LikeClockwork/LargeWordClock/KiCad/LargeKickstarter/SVG/button_section.png

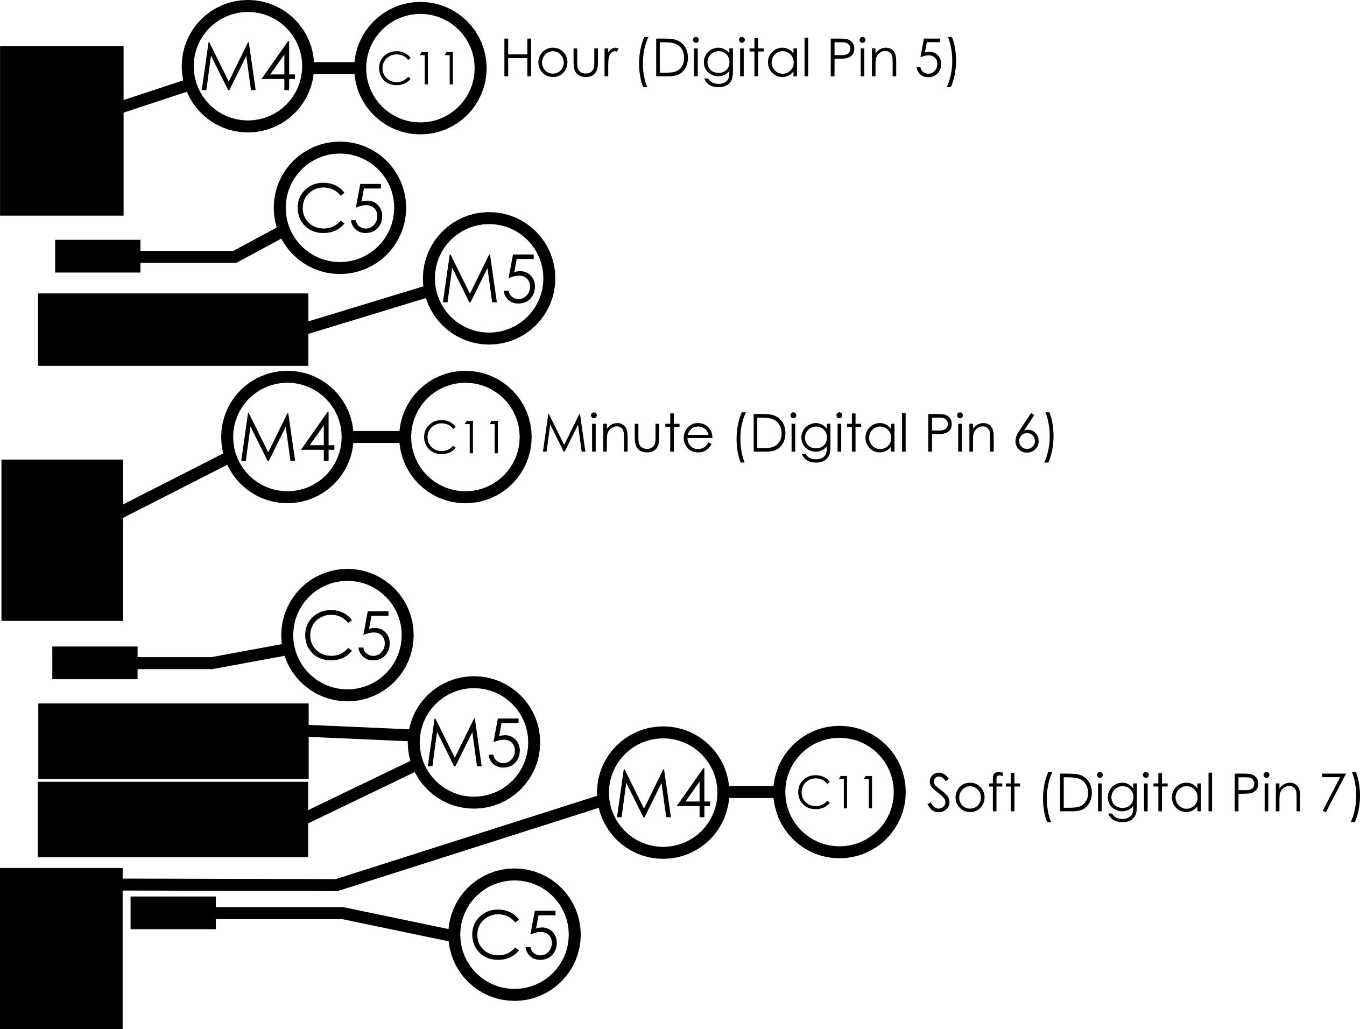
KiCad/LargeKickstarter/SVG/button_section.png
