LikeClockwork/LargeWordClock/KiCad/LargeKickstarter/SVG/Proto_area.png

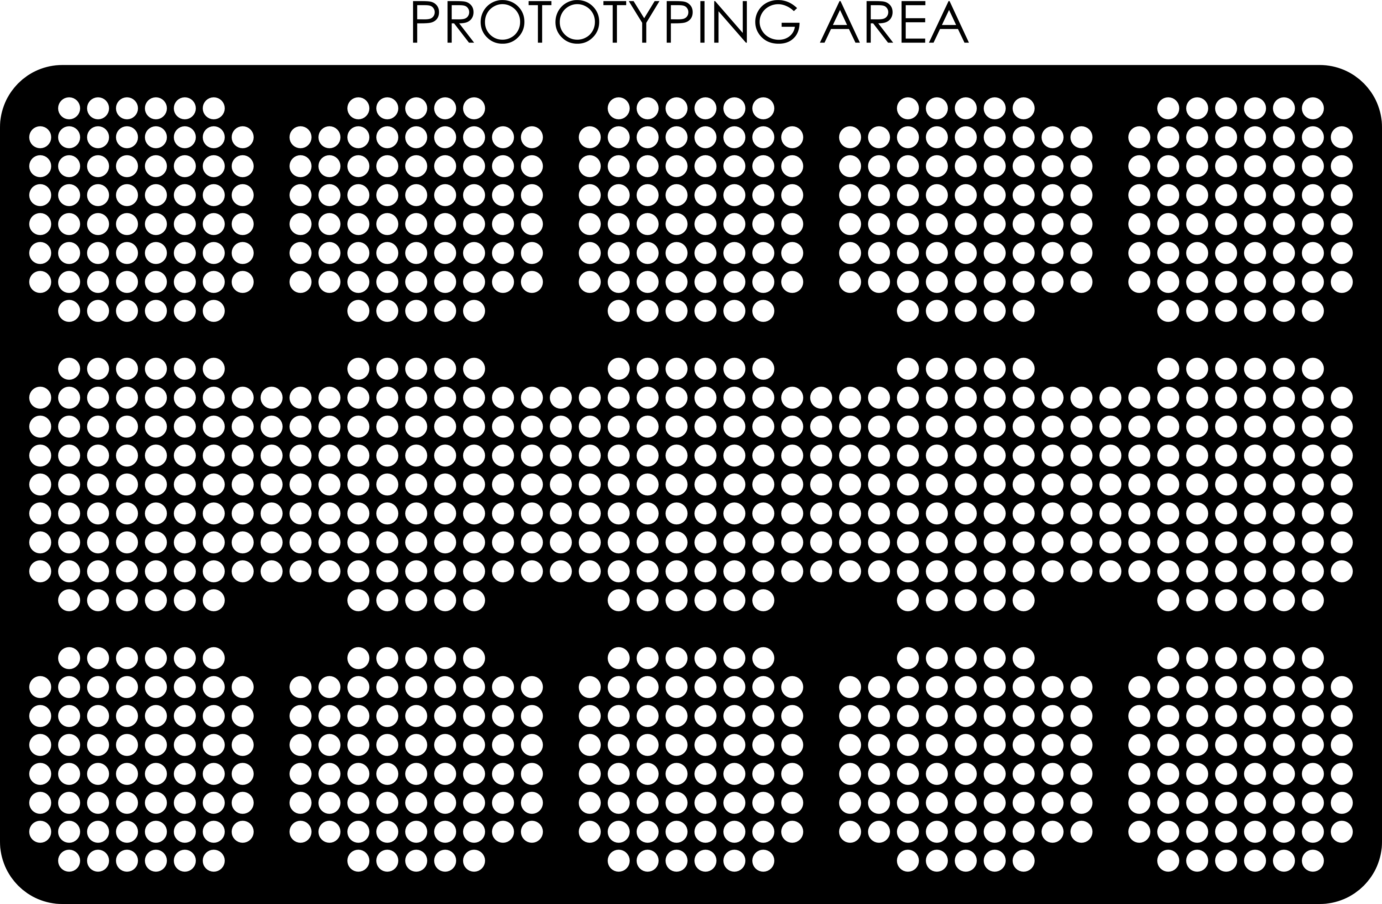
KiCad/LargeKickstarter/SVG/Proto_area.png
