LikeClockwork/LargeWordClock/KiCad/LargeKickstarter/SVG/shield_footprint.png

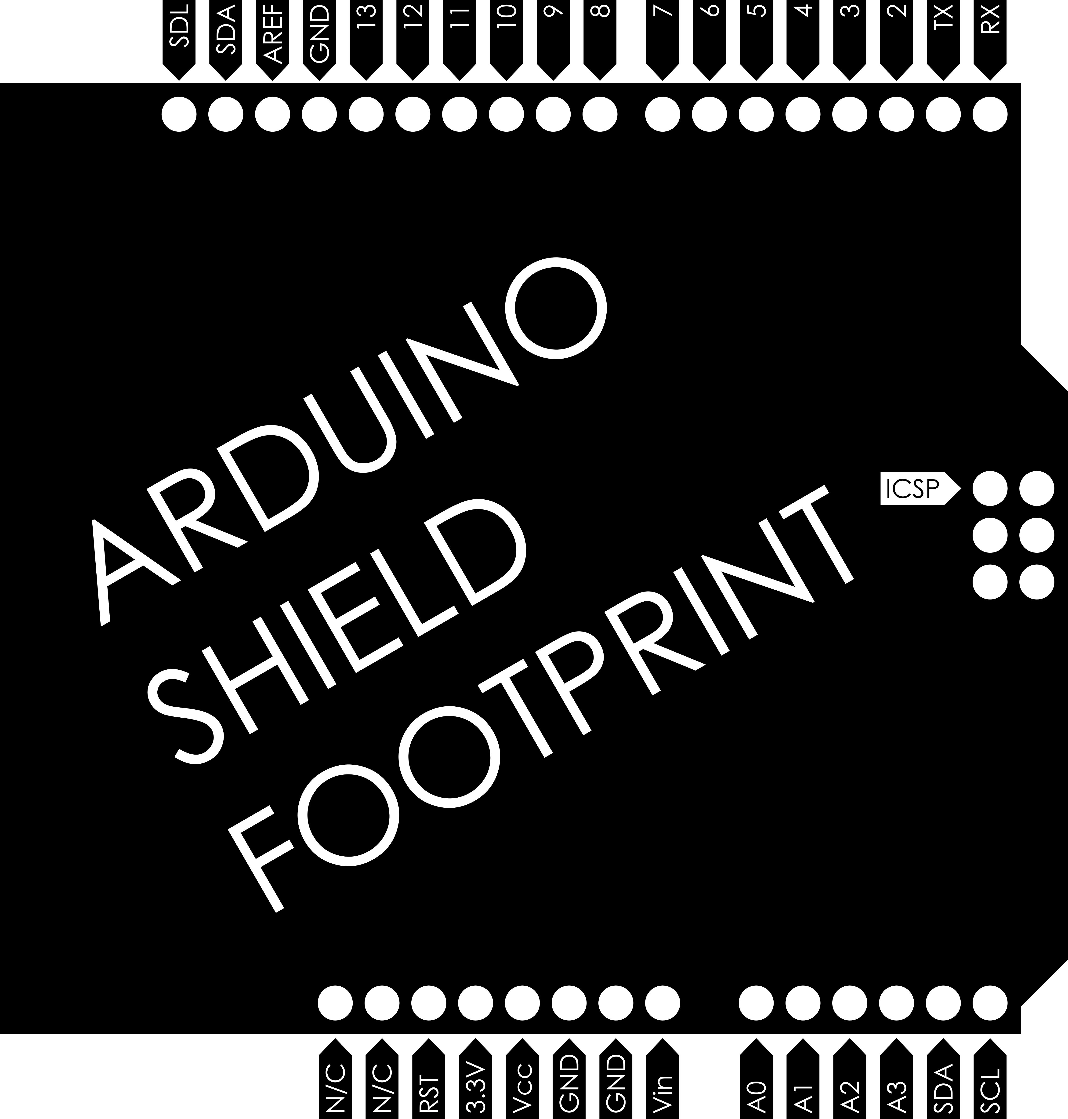
KiCad/LargeKickstarter/SVG/shield_footprint.png
