LikeClockwork/LargeWordClock/KiCad/LargeKickstarter/LargeKickstarter.sch

## KiCad design KiCad/LargeKickstarter/LargeKickstarter.sch (2015-11-24)

Schematic: LargeKickstarter.sch

Parts:
0-0, 0-1, 0-2, 0-3, 0-4, 0-5, 0-6, 0-7, 0-8, 0-9, 0-10, 0-11, 0-12, 0-13, 0-14, 0-15, 0-16, 0-17, 0-18, 0-19, 0-20, 0-21, 0-22, 0-23, 0-24, 0-25, 0-26, 0-27, 0-28, 0-29, 0-30, 0-31, 1-0, 1-1, 1-2, 1-3, 1-4, 1-5, 1-6, 1-7, 1-8, 1-9, 1-10, 1-11, 1-12, 1-13, 1-14, 1-15, 1-16, 1-17, 1-18, 1-19, 1-20, 1-21, 1-22, 1-23, 1-24, 1-25, 1-26, 1-27, 1-28, 1-29, 1-30, 1-31, 2-0, 2-1, 2-2, 2-3, 2-4, 2-5, 2-6, 2-7, 2-8, 2-9, 2-10, 2-11, 2-12, 2-13, 2-14, 2-15, 2-16, 2-17, 2-18, 2-19, 2-20, 2-21, 2-22, 2-23, 2-24, 2-25, 2-26, 2-27, 2-28, 2-29, 2-30, 2-31, 3-0, 3-1, 3-2, 3-3, 3-4, 3-5, 3-6, 3-7, 3-8, 3-9, 3-10, 3-11, 3-12, 3-13, 3-14, 3-15, 3-16, 3-17, 3-18, 3-19, 3-20, 3-21, 3-22, 3-23, 3-24, 3-25, 3-26, 3-27, 3-28, 3-29, 3-30, 3-31, 4-0, 4-1, 4-2, 4-3, 4-4, 4-5, 4-6, 4-7, 4-8, 4-9, 4-10, 4-11, 4-12, 4-13, 4-14, 4-15, 4-16, 4-17, 4-18, 4-19, 4-20, 4-21, 4-22, 4-23, 4-24, 4-25, 4-26, 4-27, 4-28, 4-29, 4-30, 4-31, 5-0, 5-1, 5-2, 5-3, 5-4, 5-5, 5-6, 5-7, 5-8, 5-9, 5-10, 5-11, 5-12, 5-13, 5-14, 5-15, 5-16, 5-17, 5-18, 5-19, 5-20, 5-21, 5-22, 5-23, 5-24, 5-25, 5-26, 5-27, 5-28, 5-29, 5-30, 5-31, 6-0, 6-1, 6-2, 6-3, 6-4, 6-5, 6-6, 6-7, 6-8, 6-9, 6-10, 6-11, 6-12, 6-13, 6-14, 6-15, 6-16, 6-17, 6-18, 6-19, 6-20, 6-21, 6-22, 6-23, 6-24, 6-25, 6-26, 6-27, 6-28, 6-29, 6-30, 6-31, 7-0, 7-1, 7-2, 7-3, 7-4, 7-5, 7-6, 7-7, 7-8, 7-9, 7-10, 7-11, 7-12, 7-13, 7-14, 7-15, 7-16, 7-17, 7-18, 7-19, 7-20, 7-21, 7-22, 7-23, 7-24, 7-25, 7-26, 7-27, 7-28, 7-29, 7-30, 7-31, 8-0, 8-1, 8-2, 8-3, 8-4, 8-5, 8-6, 8-7, 8-8, 8-9, 8-10, 8-11, 8-12, 8-13, 8-14, 8-15, 8-16, 8-17, 8-18, 8-19, 8-20, 8-21, 8-22, 8-23, 8-24, 8-25, 8-26, 8-27, 8-28, 8-29, 8-30, 8-31, 9-0, 9-1, 9-2, 9-3, 9-4, 9-5, 9-6, 9-7, 9-8, 9-9, 9-10, 9-11, 9-12, 9-13, 9-14, 9-15, 9-16, 9-17, 9-18, 9-19, 9-20, 9-21, 9-22, 9-23, 9-24, 9-25, 9-26, 9-27, 9-28, 9-29, 9-30, 9-31, 10-0, 10-1, 10-2, 10-3, 10-4, 10-5, 10-6, 10-7, 10-8, 10-9, 10-10, 10-11, 10-12, 10-13, 10-14, 10-15, 10-16, 10-17, 10-18, 10-19, 10-20, 10-21, 10-22, 10-23, 10-24, 10-25, 10-26, 10-27, 10-28, 10-29, 10-30, 10-31, 11-0, 11-1, 11-2, 11-3, 11-4, 11-5, 11-6, 11-7, 11-8, 11-9, 11-10, 11-11, 11-12, 11-13, 11-14, 11-15, 11-16, 11-17, 11-18, 11-19, 11-20, 11-21, 11-22, 11-23, 11-24, 11-25, 11-26, 11-27, 11-28, 11-29, 11-30, 11-31, 12-0, 12-1, 12-2, 12-3, 12-4, 12-5, 12-6, 12-7, 12-8, 12-9, 12-10, 12-11, 12-12, 12-13, 12-14, 12-15, 12-16, 12-17, 12-18, 12-19, 12-20, 12-21, 12-22, 12-23, 12-24, 12-25, 12-26, 12-27, 12-28, 12-29, 12-30, 12-31, 13-0, 13-1, 13-2, 13-3, 13-4, 13-5, 13-6, 13-7, 13-8, 13-9, 13-10, 13-11, 13-12, 13-13, 13-14, 13-15, 13-16, 13-17, 13-18, 13-19, 13-20, 13-21, 13-22, 13-23, 13-24, 13-25, 13-26, 13-27, 13-28, 13-29, 13-30, 13-31, 14-0, 14-1, 14-2, 14-3, 14-4, 14-5, 14-6, 14-7, 14-8, 14-9, 14-10, 14-11, 14-12, 14-13, 14-14, 14-15, 14-16, 14-17, 14-18, 14-19, 14-20, 14-21, 14-22, 14-23, 14-24, 14-25, 14-26, 14-27, 14-28, 14-29, 14-30, 14-31, 15-0, 15-1, 15-2, 15-3, 15-4, 15-5, 15-6, 15-7, 15-8, 15-9, 15-10, 15-11, 15-12, 15-13, 15-14, 15-15, 15-16, 15-17, 15-18, 15-19, 15-20, 15-21, 15-22, 15-23, 15-24, 15-25, 15-26, 15-27, 15-28, 15-29, 15-30, 15-31: LED; SMD_LED_PLCC_2
BT1: BATTERY; BATTCOM_20MM_PTH
C1, C4, C5, C6, C7, C8: 0.1uF; C_0603_HandSoldering
C2: 10uF; Elko_vert_11.2x7.5mm_RM2.5_CopperClear
C3: 1uF; Elko_vert_11.2x7.5mm_RM2.5_CopperClear
D1: DIODE; Diode-SMA_Handsoldering
D2, D3, D4, D5: DIODE; SOD-323
D6: DIODE; Diode_DO-41_SOD81_Horizontal_RM10
JP1, JP2, JP3, JP4, JP5, JP6, JP7, JP8, JP9, JP10, JP11, JP12: JUMPER; solder_jumper
P1: CONN_01X03; Diode_TO-220_Dual_CommonCathode_Horizontal_LargePads
P2: CONN_01X02; Pin_Header_Straight_1x02
P3: CONN_01X05; Pin_Header_Straight_1x05
P4: CONN_02X03; Pin_Header_Straight_2x03
P5: CONN_01X06; Pin_Header_Straight_1x06
R1, R2, R4, R5, R7: 10K; R_0603_HandSoldering
R3, R6, R8, R9, R10, R11, R12, R13, R14, R15, R16, R17: 47K; R_0603_HandSoldering
R18, R19, R20: 10K; Resistor_Horizontal_RM10mm
SW1: HOUR; TACTILE-PTH-SIDEEZ
SW2: MIN; TACTILE-PTH-SIDEEZ
SW4: SOFT; TACTILE-PTH-SIDEEZ
U1, U4, U10, U12: HT16K33; SO28W
U2: DS3231; SOIC-16_7.5x10.3mm_Pitch1.27mm
U3: ATMEGA328-TQFP; TQFP32-08
U5, U6, U9, U11: HT16K33_BOUT; HT16K33_Breakout
U7: Arduino_Nano
U8: UNO_FOOTPRINT; shield_footprint

Connections:
2: U3.32 (2), U7.5 (2), U8.30 (2)
3: U3.1 (3), U7.6 (3), U8.29 (3)
3.3V: U7.29 (3.3V), U8.4 (3.3V)
4: U3.2 (4), U7.7 (4), U8.28 (4)
5: R1.1, R18.1, SW1.2, U3.9 (5), U7.8 (5), U8.27 (5)
6: R2.1, R19.1, SW2.2, U3.10 (6), U7.9 (6), U8.26 (6)
7: R5.1, R20.1, SW4.2, U3.11 (7), U7.10 (7), U8.25 (7)
8: U3.12 (8), U7.11 (8), U8.24 (8)
9: U3.13 (9), U7.12 (9), U8.23 (9)
10: U3.14 (10), U7.13 (10/SS), U8.22 (10)
A0: U3.23 (A0), U7.27 (A0), U8.9 (A0)
A1: U3.24 (A1), U7.26 (A1), U8.10 (A1)
A2: U3.25 (A2), U7.25 (A2), U8.11 (A2)
A3: U3.26 (A3), U7.24 (A3), U8.12 (A3)
A6: U3.19 (A6), U7.21 (A6)
A7: U3.22 (A7), U7.20 (A7)
AREF: U3.20 (AREF), U7.28 (AREF), U8.17 (AREF)
COM-0-0: 0-0.2 (K), 1-0.2 (K), 2-0.2 (K), 3-0.2 (K), 4-0.2 (K), 5-0.2 (K), 6-0.2 (K), 7-0.2 (K), 8-0.2 (K), 9-0.2 (K), 10-0.2 (K), 11-0.2 (K), 12-0.2 (K), 13-0.2 (K), 14-0.2 (K), 15-0.2 (K), D3.2 (A), U1.2 (COM0/AD), U5.2 (COM0/A0)
COM-0-1: 0-1.2 (K), 1-1.2 (K), 2-1.2 (K), 3-1.2 (K), 4-1.2 (K), 5-1.2 (K), 6-1.2 (K), 7-1.2 (K), 8-1.2 (K), 9-1.2 (K), 10-1.2 (K), 11-1.2 (K), 12-1.2 (K), 13-1.2 (K), 14-1.2 (K), 15-1.2 (K), U1.3 (COM1), U5.3 (COM1)
COM-0-2: 0-2.2 (K), 1-2.2 (K), 2-2.2 (K), 3-2.2 (K), 4-2.2 (K), 5-2.2 (K), 6-2.2 (K), 7-2.2 (K), 8-2.2 (K), 9-2.2 (K), 10-2.2 (K), 11-2.2 (K), 12-2.2 (K), 13-2.2 (K), 14-2.2 (K), 15-2.2 (K), U1.4 (COM2), U5.4 (COM2)
COM-0-3: 0-3.2 (K), 1-3.2 (K), 2-3.2 (K), 3-3.2 (K), 4-3.2 (K), 5-3.2 (K), 6-3.2 (K), 7-3.2 (K), 8-3.2 (K), 9-3.2 (K), 10-3.2 (K), 11-3.2 (K), 12-3.2 (K), 13-3.2 (K), 14-3.2 (K), 15-3.2 (K), U1.5 (COM3), U5.5 (COM3)
COM-0-4: 0-4.2 (K), 1-4.2 (K), 2-4.2 (K), 3-4.2 (K), 4-4.2 (K), 5-4.2 (K), 6-4.2 (K), 7-4.2 (K), 8-4.2 (K), 9-4.2 (K), 10-4.2 (K), 11-4.2 (K), 12-4.2 (K), 13-4.2 (K), 14-4.2 (K), 15-4.2 (K), U1.6 (COM4), U5.6 (COM4)
COM-0-5: 0-5.2 (K), 1-5.2 (K), 2-5.2 (K), 3-5.2 (K), 4-5.2 (K), 5-5.2 (K), 6-5.2 (K), 7-5.2 (K), 8-5.2 (K), 9-5.2 (K), 10-5.2 (K), 11-5.2 (K), 12-5.2 (K), 13-5.2 (K), 14-5.2 (K), 15-5.2 (K), U1.7 (COM5), U5.7 (COM5)
COM-0-6: 0-6.2 (K), 1-6.2 (K), 2-6.2 (K), 3-6.2 (K), 4-6.2 (K), 5-6.2 (K), 6-6.2 (K), 7-6.2 (K), 8-6.2 (K), 9-6.2 (K), 10-6.2 (K), 11-6.2 (K), 12-6.2 (K), 13-6.2 (K), 14-6.2 (K), 15-6.2 (K), U1.8 (COM6), U5.8 (COM6)
COM-0-7: 0-7.2 (K), 1-7.2 (K), 2-7.2 (K), 3-7.2 (K), 4-7.2 (K), 5-7.2 (K), 6-7.2 (K), 7-7.2 (K), 8-7.2 (K), 9-7.2 (K), 10-7.2 (K), 11-7.2 (K), 12-7.2 (K), 13-7.2 (K), 14-7.2 (K), 15-7.2 (K), U1.9 (COM7), U5.9 (COM7)
COM-1-0: 0-8.2 (K), 1-8.2 (K), 2-8.2 (K), 3-8.2 (K), 4-8.2 (K), 5-8.2 (K), 6-8.2 (K), 7-8.2 (K), 8-8.2 (K), 9-8.2 (K), 10-8.2 (K), 11-8.2 (K), 12-8.2 (K), 13-8.2 (K), 14-8.2 (K), 15-8.2 (K), D2.2 (A), U4.2 (COM0/AD), U6.2 (COM0/A0)
COM-1-1: 0-9.2 (K), 1-9.2 (K), 2-9.2 (K), 3-9.2 (K), 4-9.2 (K), 5-9.2 (K), 6-9.2 (K), 7-9.2 (K), 8-9.2 (K), 9-9.2 (K), 10-9.2 (K), 11-9.2 (K), 12-9.2 (K), 13-9.2 (K), 14-9.2 (K), 15-9.2 (K), U4.3 (COM1), U6.3 (COM1)
COM-1-2: 0-10.2 (K), 1-10.2 (K), 2-10.2 (K), 3-10.2 (K), 4-10.2 (K), 5-10.2 (K), 6-10.2 (K), 7-10.2 (K), 8-10.2 (K), 9-10.2 (K), 10-10.2 (K), 11-10.2 (K), 12-10.2 (K), 13-10.2 (K), 14-10.2 (K), 15-10.2 (K), U4.4 (COM2), U6.4 (COM2)
COM-1-3: 0-11.2 (K), 1-11.2 (K), 2-11.2 (K), 3-11.2 (K), 4-11.2 (K), 5-11.2 (K), 6-11.2 (K), 7-11.2 (K), 8-11.2 (K), 9-11.2 (K), 10-11.2 (K), 11-11.2 (K), 12-11.2 (K), 13-11.2 (K), 14-11.2 (K), 15-11.2 (K), U4.5 (COM3), U6.5 (COM3)
COM-1-4: 0-12.2 (K), 1-12.2 (K), 2-12.2 (K), 3-12.2 (K), 4-12.2 (K), 5-12.2 (K), 6-12.2 (K), 7-12.2 (K), 8-12.2 (K), 9-12.2 (K), 10-12.2 (K), 11-12.2 (K), 12-12.2 (K), 13-12.2 (K), 14-12.2 (K), 15-12.2 (K), U4.6 (COM4), U6.6 (COM4)
COM-1-5: 0-13.2 (K), 1-13.2 (K), 2-13.2 (K), 3-13.2 (K), 4-13.2 (K), 5-13.2 (K), 6-13.2 (K), 7-13.2 (K), 8-13.2 (K), 9-13.2 (K), 10-13.2 (K), 11-13.2 (K), 12-13.2 (K), 13-13.2 (K), 14-13.2 (K), 15-13.2 (K), U4.7 (COM5), U6.7 (COM5)
COM-1-6: 0-14.2 (K), 1-14.2 (K), 2-14.2 (K), 3-14.2 (K), 4-14.2 (K), 5-14.2 (K), 6-14.2 (K), 7-14.2 (K), 8-14.2 (K), 9-14.2 (K), 10-14.2 (K), 11-14.2 (K), 12-14.2 (K), 13-14.2 (K), 14-14.2 (K), 15-14.2 (K), U4.8 (COM6), U6.8 (COM6)
COM-1-7: 0-15.2 (K), 1-15.2 (K), 2-15.2 (K), 3-15.2 (K), 4-15.2 (K), 5-15.2 (K), 6-15.2 (K), 7-15.2 (K), 8-15.2 (K), 9-15.2 (K), 10-15.2 (K), 11-15.2 (K), 12-15.2 (K), 13-15.2 (K), 14-15.2 (K), 15-15.2 (K), U4.9 (COM7), U6.9 (COM7)
COM-2-0: 0-16.2 (K), 1-16.2 (K), 2-16.2 (K), 3-16.2 (K), 4-16.2 (K), 5-16.2 (K), 6-16.2 (K), 7-16.2 (K), 8-16.2 (K), 9-16.2 (K), 10-16.2 (K), 11-16.2 (K), 12-16.2 (K), 13-16.2 (K), 14-16.2 (K), 15-16.2 (K), D4.2 (A), U9.2 (COM0/A0), U10.2 (COM0/AD)
COM-2-1: 0-17.2 (K), 1-17.2 (K), 2-17.2 (K), 3-17.2 (K), 4-17.2 (K), 5-17.2 (K), 6-17.2 (K), 7-17.2 (K), 8-17.2 (K), 9-17.2 (K), 10-17.2 (K), 11-17.2 (K), 12-17.2 (K), 13-17.2 (K), 14-17.2 (K), 15-17.2 (K), U9.3 (COM1), U10.3 (COM1)
COM-2-2: 0-18.2 (K), 1-18.2 (K), 2-18.2 (K), 3-18.2 (K), 4-18.2 (K), 5-18.2 (K), 6-18.2 (K), 7-18.2 (K), 8-18.2 (K), 9-18.2 (K), 10-18.2 (K), 11-18.2 (K), 12-18.2 (K), 13-18.2 (K), 14-18.2 (K), 15-18.2 (K), U9.4 (COM2), U10.4 (COM2)
COM-2-3: 0-19.2 (K), 1-19.2 (K), 2-19.2 (K), 3-19.2 (K), 4-19.2 (K), 5-19.2 (K), 6-19.2 (K), 7-19.2 (K), 8-19.2 (K), 9-19.2 (K), 10-19.2 (K), 11-19.2 (K), 12-19.2 (K), 13-19.2 (K), 14-19.2 (K), 15-19.2 (K), U9.5 (COM3), U10.5 (COM3)
COM-2-4: 0-20.2 (K), 1-20.2 (K), 2-20.2 (K), 3-20.2 (K), 4-20.2 (K), 5-20.2 (K), 6-20.2 (K), 7-20.2 (K), 8-20.2 (K), 9-20.2 (K), 10-20.2 (K), 11-20.2 (K), 12-20.2 (K), 13-20.2 (K), 14-20.2 (K), 15-20.2 (K), U9.6 (COM4), U10.6 (COM4)
COM-2-5: 0-21.2 (K), 1-21.2 (K), 2-21.2 (K), 3-21.2 (K), 4-21.2 (K), 5-21.2 (K), 6-21.2 (K), 7-21.2 (K), 8-21.2 (K), 9-21.2 (K), 10-21.2 (K), 11-21.2 (K), 12-21.2 (K), 13-21.2 (K), 14-21.2 (K), 15-21.2 (K), U9.7 (COM5), U10.7 (COM5)
COM-2-6: 0-22.2 (K), 1-22.2 (K), 2-22.2 (K), 3-22.2 (K), 4-22.2 (K), 5-22.2 (K), 6-22.2 (K), 7-22.2 (K), 8-22.2 (K), 9-22.2 (K), 10-22.2 (K), 11-22.2 (K), 12-22.2 (K), 13-22.2 (K), 14-22.2 (K), 15-22.2 (K), U9.8 (COM6), U10.8 (COM6)
COM-2-7: 0-23.2 (K), 1-23.2 (K), 2-23.2 (K), 3-23.2 (K), 4-23.2 (K), 5-23.2 (K), 6-23.2 (K), 7-23.2 (K), 8-23.2 (K), 9-23.2 (K), 10-23.2 (K), 11-23.2 (K), 12-23.2 (K), 13-23.2 (K), 14-23.2 (K), 15-23.2 (K), U9.9 (COM7), U10.9 (COM7)
COM-3-0: 0-24.2 (K), 1-24.2 (K), 2-24.2 (K), 3-24.2 (K), 4-24.2 (K), 5-24.2 (K), 6-24.2 (K), 7-24.2 (K), 8-24.2 (K), 9-24.2 (K), 10-24.2 (K), 11-24.2 (K), 12-24.2 (K), 13-24.2 (K), 14-24.2 (K), 15-24.2 (K), D5.2 (A), U11.2 (COM0/A0), U12.2 (COM0/AD)
COM-3-1: 0-25.2 (K), 1-25.2 (K), 2-25.2 (K), 3-25.2 (K), 4-25.2 (K), 5-25.2 (K), 6-25.2 (K), 7-25.2 (K), 8-25.2 (K), 9-25.2 (K), 10-25.2 (K), 11-25.2 (K), 12-25.2 (K), 13-25.2 (K), 14-25.2 (K), 15-25.2 (K), U11.3 (COM1), U12.3 (COM1)
COM-3-2: 0-26.2 (K), 1-26.2 (K), 2-26.2 (K), 3-26.2 (K), 4-26.2 (K), 5-26.2 (K), 6-26.2 (K), 7-26.2 (K), 8-26.2 (K), 9-26.2 (K), 10-26.2 (K), 11-26.2 (K), 12-26.2 (K), 13-26.2 (K), 14-26.2 (K), 15-26.2 (K), U11.4 (COM2), U12.4 (COM2)
COM-3-3: 0-27.2 (K), 1-27.2 (K), 2-27.2 (K), 3-27.2 (K), 4-27.2 (K), 5-27.2 (K), 6-27.2 (K), 7-27.2 (K), 8-27.2 (K), 9-27.2 (K), 10-27.2 (K), 11-27.2 (K), 12-27.2 (K), 13-27.2 (K), 14-27.2 (K), 15-27.2 (K), U11.5 (COM3), U12.5 (COM3)
COM-3-4: 0-28.2 (K), 1-28.2 (K), 2-28.2 (K), 3-28.2 (K), 4-28.2 (K), 5-28.2 (K), 6-28.2 (K), 7-28.2 (K), 8-28.2 (K), 9-28.2 (K), 10-28.2 (K), 11-28.2 (K), 12-28.2 (K), 13-28.2 (K), 14-28.2 (K), 15-28.2 (K), U11.6 (COM4), U12.6 (COM4)
COM-3-5: 0-29.2 (K), 1-29.2 (K), 2-29.2 (K), 3-29.2 (K), 4-29.2 (K), 5-29.2 (K), 6-29.2 (K), 7-29.2 (K), 8-29.2 (K), 9-29.2 (K), 10-29.2 (K), 11-29.2 (K), 12-29.2 (K), 13-29.2 (K), 14-29.2 (K), 15-29.2 (K), U11.7 (COM5), U12.7 (COM5)
COM-3-6: 0-30.2 (K), 1-30.2 (K), 2-30.2 (K), 3-30.2 (K), 4-30.2 (K), 5-30.2 (K), 6-30.2 (K), 7-30.2 (K), 8-30.2 (K), 9-30.2 (K), 10-30.2 (K), 11-30.2 (K), 12-30.2 (K), 13-30.2 (K), 14-30.2 (K), 15-30.2 (K), U11.8 (COM6), U12.8 (COM6)
COM-3-7: 0-31.2 (K), 1-31.2 (K), 2-31.2 (K), 3-31.2 (K), 4-31.2 (K), 5-31.2 (K), 6-31.2 (K), 7-31.2 (K), 8-31.2 (K), 9-31.2 (K), 10-31.2 (K), 11-31.2 (K), 12-31.2 (K), 13-31.2 (K), 14-31.2 (K), 15-31.2 (K), U11.9 (COM7), U12.9 (COM7)
GND: BT1.2 (-), C1.2, C2.2, C3.2, C4.2, C5.2, C6.2, C7.2, C8.2, P1.2, P2.1, P3.GND (P5), P4.6, P5.6, R1.2, R2.2, R5.2, R18.2, R19.2, R20.2, U1.1 (GND), U2.5 (N/C), U2.6 (N/C), U2.7 (N/C), U2.8 (N/C), U2.9 (N/C), U2.10 (N/C), U2.11 (N/C), U2.12 (N/C), U2.13 (GND), U3.3 (GND), U3.5 (GND), U3.21 (GND), U4.1 (GND), U5.1 (GND), U6.1 (GND), U7.4 (GND), U7.17 (GND), U8.6 (GND), U8.7 (GND), U8.18 (GND), U8.38 (GND), U9.1 (GND), U10.1 (GND), U11.1 (GND), U12.1 (GND)
MISO: P4.1, U3.16 (12/MISO), U7.15 (12/MISO), U8.20 (12), U8.35 (MISO)
MOSI: P4.4, U3.15 (11/MOSI), U7.14 (11/MOSI), U8.21 (11), U8.37 (MOSI)
unnamed: BT1.1 (+), U2.14 (Vbat)
unnamed: D2.1 (K), R9.2, R10.2, R11.2
unnamed: D3.1 (K), R3.2, R6.2, R8.2
unnamed: D4.1 (K), R12.2, R13.2, R14.2
unnamed: D5.1 (K), R15.2, R16.2, R17.2
unnamed: JP1.1, R3.1
unnamed: JP2.1, R6.1
unnamed: JP3.1, R8.1
unnamed: JP4.1, R11.1
unnamed: JP5.1, R9.1
unnamed: JP6.1, R10.1
unnamed: JP7.1, R12.1
unnamed: JP8.1, R13.1
unnamed: JP9.1, R14.1
unnamed: JP10.1, R15.1
unnamed: JP11.1, R16.1
unnamed: JP12.1, R17.1
ROW-0-0: 0-0.1 (A), 0-1.1 (A), 0-2.1 (A), 0-3.1 (A), 0-4.1 (A), 0-5.1 (A), 0-6.1 (A), 0-7.1 (A), JP1.2, U1.25 (ROW0/A2), U5.25 (ROW0/A2)
ROW-0-1: 1-0.1 (A), 1-1.1 (A), 1-2.1 (A), 1-3.1 (A), 1-4.1 (A), 1-5.1 (A), 1-6.1 (A), 1-7.1 (A), JP2.2, U1.24 (ROW1/A1), U5.24 (ROW1/A1)
ROW-0-2: 2-0.1 (A), 2-1.1 (A), 2-2.1 (A), 2-3.1 (A), 2-4.1 (A), 2-5.1 (A), 2-6.1 (A), 2-7.1 (A), JP3.2, U1.23 (ROW2/A0), U5.23 (ROW2/A0)
ROW-0-3: 3-0.1 (A), 3-1.1 (A), 3-2.1 (A), 3-3.1 (A), 3-4.1 (A), 3-5.1 (A), 3-6.1 (A), 3-7.1 (A), U1.22 (ROW3), U5.22 (ROW3)
ROW-0-4: 4-0.1 (A), 4-1.1 (A), 4-2.1 (A), 4-3.1 (A), 4-4.1 (A), 4-5.1 (A), 4-6.1 (A), 4-7.1 (A), U1.21 (ROW4), U5.21 (ROW4)
ROW-0-5: 5-0.1 (A), 5-1.1 (A), 5-2.1 (A), 5-3.1 (A), 5-4.1 (A), 5-5.1 (A), 5-6.1 (A), 5-7.1 (A), U1.20 (ROW5), U5.20 (ROW5)
ROW-0-6: 6-0.1 (A), 6-1.1 (A), 6-2.1 (A), 6-3.1 (A), 6-4.1 (A), 6-5.1 (A), 6-6.1 (A), 6-7.1 (A), U1.19 (ROW6), U5.19 (ROW6)
ROW-0-7: 7-0.1 (A), 7-1.1 (A), 7-2.1 (A), 7-3.1 (A), 7-4.1 (A), 7-5.1 (A), 7-6.1 (A), 7-7.1 (A), U1.18 (ROW7), U5.18 (ROW7)
ROW-0-8: 8-0.1 (A), 8-1.1 (A), 8-2.1 (A), 8-3.1 (A), 8-4.1 (A), 8-5.1 (A), 8-6.1 (A), 8-7.1 (A), U1.17 (ROW8), U5.17 (ROW8)
ROW-0-9: 9-0.1 (A), 9-1.1 (A), 9-2.1 (A), 9-3.1 (A), 9-4.1 (A), 9-5.1 (A), 9-6.1 (A), 9-7.1 (A), U1.16 (ROW9), U5.16 (ROW9)
ROW-0-10: 10-0.1 (A), 10-1.1 (A), 10-2.1 (A), 10-3.1 (A), 10-4.1 (A), 10-5.1 (A), 10-6.1 (A), 10-7.1 (A), U1.15 (ROW10), U5.15 (ROW10)
ROW-0-11: 11-0.1 (A), 11-1.1 (A), 11-2.1 (A), 11-3.1 (A), 11-4.1 (A), 11-5.1 (A), 11-6.1 (A), 11-7.1 (A), U1.14 (ROW11), U5.14 (ROW11)
ROW-0-12: 12-0.1 (A), 12-1.1 (A), 12-2.1 (A), 12-3.1 (A), 12-4.1 (A), 12-5.1 (A), 12-6.1 (A), 12-7.1 (A), U1.13 (ROW12), U5.13 (ROW12)
ROW-0-13: 13-0.1 (A), 13-1.1 (A), 13-2.1 (A), 13-3.1 (A), 13-4.1 (A), 13-5.1 (A), 13-6.1 (A), 13-7.1 (A), U1.12 (ROW13), U5.12 (ROW13)
ROW-0-14: 14-0.1 (A), 14-1.1 (A), 14-2.1 (A), 14-3.1 (A), 14-4.1 (A), 14-5.1 (A), 14-6.1 (A), 14-7.1 (A), U1.11 (ROW14), U5.11 (ROW14)
ROW-0-15: 15-0.1 (A), 15-1.1 (A), 15-2.1 (A), 15-3.1 (A), 15-4.1 (A), 15-5.1 (A), 15-6.1 (A), 15-7.1 (A), U1.10 (ROW15), U5.10 (ROW15)
ROW-1-0: 0-8.1 (A), 0-9.1 (A), 0-10.1 (A), 0-11.1 (A), 0-12.1 (A), 0-13.1 (A), 0-14.1 (A), 0-15.1 (A), JP4.2, U4.25 (ROW0/A2), U6.25 (ROW0/A2)
ROW-1-1: 1-8.1 (A), 1-9.1 (A), 1-10.1 (A), 1-11.1 (A), 1-12.1 (A), 1-13.1 (A), 1-14.1 (A), 1-15.1 (A), JP5.2, U4.24 (ROW1/A1), U6.24 (ROW1/A1)
ROW-1-2: 2-8.1 (A), 2-9.1 (A), 2-10.1 (A), 2-11.1 (A), 2-12.1 (A), 2-13.1 (A), 2-14.1 (A), 2-15.1 (A), JP6.2, U4.23 (ROW2/A0), U6.23 (ROW2/A0)
ROW-1-3: 3-8.1 (A), 3-9.1 (A), 3-10.1 (A), 3-11.1 (A), 3-12.1 (A), 3-13.1 (A), 3-14.1 (A), 3-15.1 (A), U4.22 (ROW3), U6.22 (ROW3)
ROW-1-4: 4-8.1 (A), 4-9.1 (A), 4-10.1 (A), 4-11.1 (A), 4-12.1 (A), 4-13.1 (A), 4-14.1 (A), 4-15.1 (A), U4.21 (ROW4), U6.21 (ROW4)
ROW-1-5: 5-8.1 (A), 5-9.1 (A), 5-10.1 (A), 5-11.1 (A), 5-12.1 (A), 5-13.1 (A), 5-14.1 (A), 5-15.1 (A), U4.20 (ROW5), U6.20 (ROW5)
ROW-1-6: 6-8.1 (A), 6-9.1 (A), 6-10.1 (A), 6-11.1 (A), 6-12.1 (A), 6-13.1 (A), 6-14.1 (A), 6-15.1 (A), U4.19 (ROW6), U6.19 (ROW6)
ROW-1-7: 7-8.1 (A), 7-9.1 (A), 7-10.1 (A), 7-11.1 (A), 7-12.1 (A), 7-13.1 (A), 7-14.1 (A), 7-15.1 (A), U4.18 (ROW7), U6.18 (ROW7)
ROW-1-8: 8-8.1 (A), 8-9.1 (A), 8-10.1 (A), 8-11.1 (A), 8-12.1 (A), 8-13.1 (A), 8-14.1 (A), 8-15.1 (A), U4.17 (ROW8), U6.17 (ROW8)
ROW-1-9: 9-8.1 (A), 9-9.1 (A), 9-10.1 (A), 9-11.1 (A), 9-12.1 (A), 9-13.1 (A), 9-14.1 (A), 9-15.1 (A), U4.16 (ROW9), U6.16 (ROW9)
ROW-1-10: 10-8.1 (A), 10-9.1 (A), 10-10.1 (A), 10-11.1 (A), 10-12.1 (A), 10-13.1 (A), 10-14.1 (A), 10-15.1 (A), U4.15 (ROW10), U6.15 (ROW10)
ROW-1-11: 11-8.1 (A), 11-9.1 (A), 11-10.1 (A), 11-11.1 (A), 11-12.1 (A), 11-13.1 (A), 11-14.1 (A), 11-15.1 (A), U4.14 (ROW11), U6.14 (ROW11)
ROW-1-12: 12-8.1 (A), 12-9.1 (A), 12-10.1 (A), 12-11.1 (A), 12-12.1 (A), 12-13.1 (A), 12-14.1 (A), 12-15.1 (A), U4.13 (ROW12), U6.13 (ROW12)
ROW-1-13: 13-8.1 (A), 13-9.1 (A), 13-10.1 (A), 13-11.1 (A), 13-12.1 (A), 13-13.1 (A), 13-14.1 (A), 13-15.1 (A), U4.12 (ROW13), U6.12 (ROW13)
ROW-1-14: 14-8.1 (A), 14-9.1 (A), 14-10.1 (A), 14-11.1 (A), 14-12.1 (A), 14-13.1 (A), 14-14.1 (A), 14-15.1 (A), U4.11 (ROW14), U6.11 (ROW14)
ROW-1-15: 15-8.1 (A), 15-9.1 (A), 15-10.1 (A), 15-11.1 (A), 15-12.1 (A), 15-13.1 (A), 15-14.1 (A), 15-15.1 (A), U4.10 (ROW15), U6.10 (ROW15)
ROW-2-0: 0-16.1 (A), 0-17.1 (A), 0-18.1 (A), 0-19.1 (A), 0-20.1 (A), 0-21.1 (A), 0-22.1 (A), 0-23.1 (A), JP7.2, U9.25 (ROW0/A2), U10.25 (ROW0/A2)
ROW-2-1: 1-16.1 (A), 1-17.1 (A), 1-18.1 (A), 1-19.1 (A), 1-20.1 (A), 1-21.1 (A), 1-22.1 (A), 1-23.1 (A), JP8.2, U9.24 (ROW1/A1), U10.24 (ROW1/A1)
ROW-2-2: 2-16.1 (A), 2-17.1 (A), 2-18.1 (A), 2-19.1 (A), 2-20.1 (A), 2-21.1 (A), 2-22.1 (A), 2-23.1 (A), JP9.2, U9.23 (ROW2/A0), U10.23 (ROW2/A0)
ROW-2-3: 3-16.1 (A), 3-17.1 (A), 3-18.1 (A), 3-19.1 (A), 3-20.1 (A), 3-21.1 (A), 3-22.1 (A), 3-23.1 (A), U9.22 (ROW3), U10.22 (ROW3)
ROW-2-4: 4-16.1 (A), 4-17.1 (A), 4-18.1 (A), 4-19.1 (A), 4-20.1 (A), 4-21.1 (A), 4-22.1 (A), 4-23.1 (A), U9.21 (ROW4), U10.21 (ROW4)
ROW-2-5: 5-16.1 (A), 5-17.1 (A), 5-18.1 (A), 5-19.1 (A), 5-20.1 (A), 5-21.1 (A), 5-22.1 (A), 5-23.1 (A), U9.20 (ROW5), U10.20 (ROW5)
ROW-2-6: 6-16.1 (A), 6-17.1 (A), 6-18.1 (A), 6-19.1 (A), 6-20.1 (A), 6-21.1 (A), 6-22.1 (A), 6-23.1 (A), U9.19 (ROW6), U10.19 (ROW6)
ROW-2-7: 7-16.1 (A), 7-17.1 (A), 7-18.1 (A), 7-19.1 (A), 7-20.1 (A), 7-21.1 (A), 7-22.1 (A), 7-23.1 (A), U9.18 (ROW7), U10.18 (ROW7)
ROW-2-8: 8-16.1 (A), 8-17.1 (A), 8-18.1 (A), 8-19.1 (A), 8-20.1 (A), 8-21.1 (A), 8-22.1 (A), 8-23.1 (A), U9.17 (ROW8), U10.17 (ROW8)
ROW-2-9: 9-16.1 (A), 9-17.1 (A), 9-18.1 (A), 9-19.1 (A), 9-20.1 (A), 9-21.1 (A), 9-22.1 (A), 9-23.1 (A), U9.16 (ROW9), U10.16 (ROW9)
ROW-2-10: 10-16.1 (A), 10-17.1 (A), 10-18.1 (A), 10-19.1 (A), 10-20.1 (A), 10-21.1 (A), 10-22.1 (A), 10-23.1 (A), U9.15 (ROW10), U10.15 (ROW10)
ROW-2-11: 11-16.1 (A), 11-17.1 (A), 11-18.1 (A), 11-19.1 (A), 11-20.1 (A), 11-21.1 (A), 11-22.1 (A), 11-23.1 (A), U9.14 (ROW11), U10.14 (ROW11)
ROW-2-12: 12-16.1 (A), 12-17.1 (A), 12-18.1 (A), 12-19.1 (A), 12-20.1 (A), 12-21.1 (A), 12-22.1 (A), 12-23.1 (A), U9.13 (ROW12), U10.13 (ROW12)
ROW-2-13: 13-16.1 (A), 13-17.1 (A), 13-18.1 (A), 13-19.1 (A), 13-20.1 (A), 13-21.1 (A), 13-22.1 (A), 13-23.1 (A), U9.12 (ROW13), U10.12 (ROW13)
ROW-2-14: 14-16.1 (A), 14-17.1 (A), 14-18.1 (A), 14-19.1 (A), 14-20.1 (A), 14-21.1 (A), 14-22.1 (A), 14-23.1 (A), U9.11 (ROW14), U10.11 (ROW14)
ROW-2-15: 15-16.1 (A), 15-17.1 (A), 15-18.1 (A), 15-19.1 (A), 15-20.1 (A), 15-21.1 (A), 15-22.1 (A), 15-23.1 (A), U9.10 (ROW15), U10.10 (ROW15)
ROW-3-0: 0-24.1 (A), 0-25.1 (A), 0-26.1 (A), 0-27.1 (A), 0-28.1 (A), 0-29.1 (A), 0-30.1 (A), 0-31.1 (A), JP10.2, U11.25 (ROW0/A2), U12.25 (ROW0/A2)
ROW-3-1: 1-24.1 (A), 1-25.1 (A), 1-26.1 (A), 1-27.1 (A), 1-28.1 (A), 1-29.1 (A), 1-30.1 (A), 1-31.1 (A), JP11.2, U11.24 (ROW1/A1), U12.24 (ROW1/A1)
ROW-3-2: 2-24.1 (A), 2-25.1 (A), 2-26.1 (A), 2-27.1 (A), 2-28.1 (A), 2-29.1 (A), 2-30.1 (A), 2-31.1 (A), JP12.2, U11.23 (ROW2/A0), U12.23 (ROW2/A0)
ROW-3-3: 3-24.1 (A), 3-25.1 (A), 3-26.1 (A), 3-27.1 (A), 3-28.1 (A), 3-29.1 (A), 3-30.1 (A), 3-31.1 (A), U11.22 (ROW3), U12.22 (ROW3)
ROW-3-4: 4-24.1 (A), 4-25.1 (A), 4-26.1 (A), 4-27.1 (A), 4-28.1 (A), 4-29.1 (A), 4-30.1 (A), 4-31.1 (A), U11.21 (ROW4), U12.21 (ROW4)
ROW-3-5: 5-24.1 (A), 5-25.1 (A), 5-26.1 (A), 5-27.1 (A), 5-28.1 (A), 5-29.1 (A), 5-30.1 (A), 5-31.1 (A), U11.20 (ROW5), U12.20 (ROW5)
ROW-3-6: 6-24.1 (A), 6-25.1 (A), 6-26.1 (A), 6-27.1 (A), 6-28.1 (A), 6-29.1 (A), 6-30.1 (A), 6-31.1 (A), U11.19 (ROW6), U12.19 (ROW6)
ROW-3-7: 7-24.1 (A), 7-25.1 (A), 7-26.1 (A), 7-27.1 (A), 7-28.1 (A), 7-29.1 (A), 7-30.1 (A), 7-31.1 (A), U11.18 (ROW7), U12.18 (ROW7)
ROW-3-8: 8-24.1 (A), 8-25.1 (A), 8-26.1 (A), 8-27.1 (A), 8-28.1 (A), 8-29.1 (A), 8-30.1 (A), 8-31.1 (A), U11.17 (ROW8), U12.17 (ROW8)
ROW-3-9: 9-24.1 (A), 9-25.1 (A), 9-26.1 (A), 9-27.1 (A), 9-28.1 (A), 9-29.1 (A), 9-30.1 (A), 9-31.1 (A), U11.16 (ROW9), U12.16 (ROW9)
ROW-3-10: 10-24.1 (A), 10-25.1 (A), 10-26.1 (A), 10-27.1 (A), 10-28.1 (A), 10-29.1 (A), 10-30.1 (A), 10-31.1 (A), U11.15 (ROW10), U12.15 (ROW10)
ROW-3-11: 11-24.1 (A), 11-25.1 (A), 11-26.1 (A), 11-27.1 (A), 11-28.1 (A), 11-29.1 (A), 11-30.1 (A), 11-31.1 (A), U11.14 (ROW11), U12.14 (ROW11)
ROW-3-12: 12-24.1 (A), 12-25.1 (A), 12-26.1 (A), 12-27.1 (A), 12-28.1 (A), 12-29.1 (A), 12-30.1 (A), 12-31.1 (A), U11.13 (ROW12), U12.13 (ROW12)
ROW-3-13: 13-24.1 (A), 13-25.1 (A), 13-26.1 (A), 13-27.1 (A), 13-28.1 (A), 13-29.1 (A), 13-30.1 (A), 13-31.1 (A), U11.12 (ROW13), U12.12 (ROW13)
ROW-3-14: 14-24.1 (A), 14-25.1 (A), 14-26.1 (A), 14-27.1 (A), 14-28.1 (A), 14-29.1 (A), 14-30.1 (A), 14-31.1 (A), U11.11 (ROW14), U12.11 (ROW14)
ROW-3-15: 15-24.1 (A), 15-25.1 (A), 15-26.1 (A), 15-27.1 (A), 15-28.1 (A), 15-29.1 (A), 15-30.1 (A), 15-31.1 (A), U11.10 (ROW15), U12.10 (ROW15)
RST: P4.5, U3.29 (RST), U7.3 (RST), U7.18 (RST), U8.3 (RESET), U8.33 (RESET)
RX: U3.30 (0/RX), U7.2 (RX), U8.32 (RX)
SCK: P4.3, U3.17 (13/SCK), U7.30 (13/SCK), U8.19 (13), U8.34 (SCK)
SCL: P3.SCL, P5.3, R4.2, U1.26 (SCL), U2.16 (SCL), U3.28 (A5/SCL), U4.26 (SCL), U5.26 (SCL), U6.26 (SCL), U7.22 (A5/SCL), U8.14 (A5), U8.15 (SCL), U9.26 (SCL), U10.26 (SCL), U11.26 (SCL), U12.26 (SCL)
SDA: P3.SDA, P5.4, R7.1, U1.27 (SDA), U2.15 (SDA), U3.27 (A4/SDA), U4.27 (SDA), U5.27 (SDA), U6.27 (SDA), U7.23 (A4/SDA), U8.13 (A4), U8.16 (SDA), U9.27 (SDA), U10.27 (SDA), U11.27 (SDA), U12.27 (SDA)
TX: U3.31 (1/TX), U7.1 (TX), U8.31 (TX)
Vcc: C1.1, C3.1, C4.1, C5.1, C6.1, C7.1, C8.1, P1.3, P3.VCC, P4.2, P5.5, R4.1, R7.2, SW1.1, SW2.1, SW4.1, U1.28 (Vcc), U2.2 (Vcc), U3.4 (VCC), U3.6 (VCC), U3.18 (AVCC), U4.28 (Vcc), U5.28 (VCC), U6.28 (VCC), U7.19 (5V), U8.5 (5V), U8.36 (5V), U9.28 (VCC), U10.28 (Vcc), U11.28 (VCC), U12.28 (Vcc)
Vin: C2.1, D1.1 (K), D6.1 (K), P1.1, U7.16 (VIN), U8.8 (VIN)
Vraw: D1.2 (A), D6.2 (A), P2.2
